jamessa/Pragmatic/Pragmatic42/MX/README.md

The Pragmatic 42 keyboard features

- 21 keys per hand with a fully symmetric double side design. One side is designed for the left hand and the other for the right.
- Duplex Matrix to save pins. Use Controller A.
-  8-pin connector that utilizes a user-friendly 2x4 2.54mm PinHeader.
- Support Kailh hotswap sockets.
- A modern 19mm x 19mm key pitch.
- Supports Kailh PG12800 Half key switch.

Current status: initing.

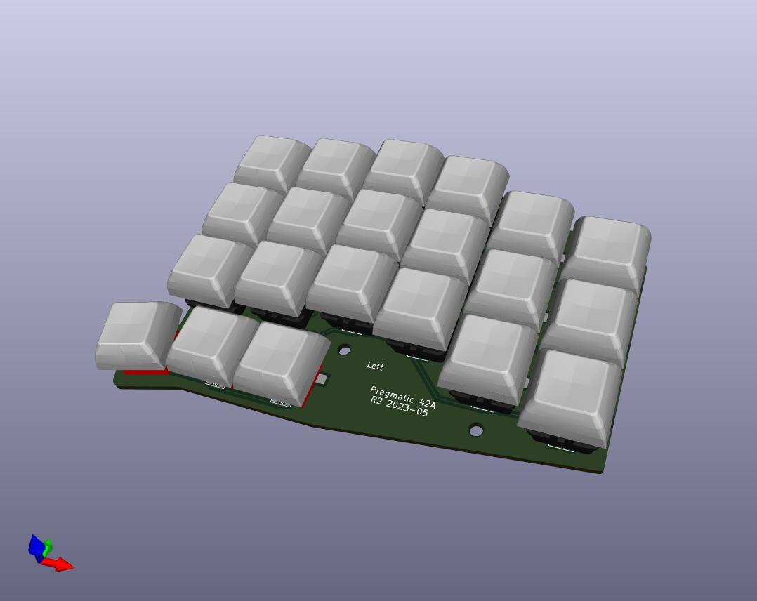
[picture p13: Pragmatic42/MX/PCB.jpg]
PCB


# Revsions
## MX42A2 2023-05-23
   ^^ Swith type MX or Choc
     ^^ Number of keys
       ^ Matrix Type: null for naïve matrix, A for duplex matrix
        ^ PCB Revision
- fix SW18, SW19 position. They were off by 0.4mm
- Stagger Profile MX V3
