jamessa/Pragmatic/layout/yapin_34/Pragmatic_60_Layer0.png

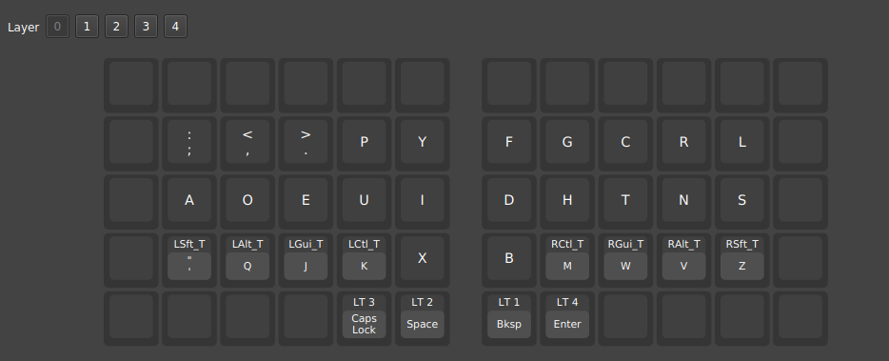
layout/yapin_34/Pragmatic_60_Layer0.png
