jamessa/Pragmatic/layout/yapin_34/Pragmatic_60_Layer1.png

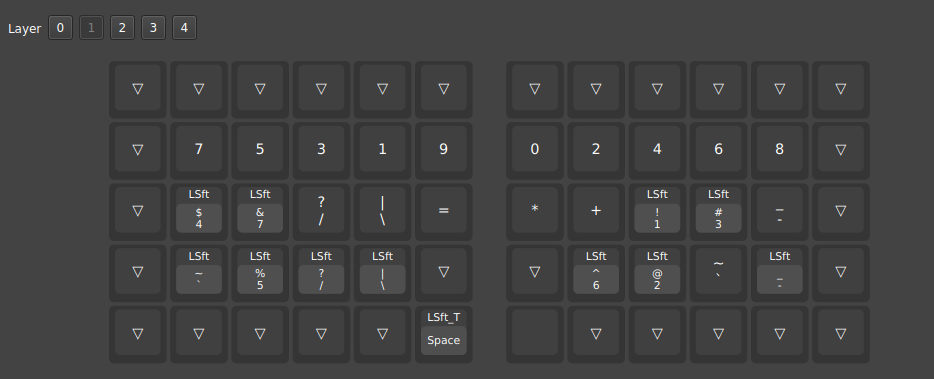
layout/yapin_34/Pragmatic_60_Layer1.png
