jamessa/Pragmatic/layout/yapin_34/Pragmatic_60_Layer2.png

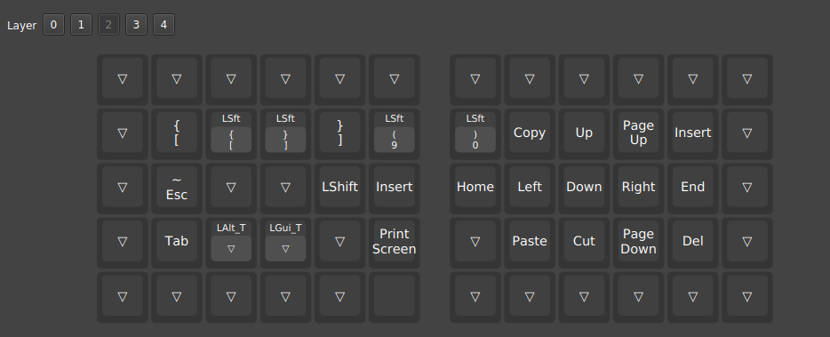
layout/yapin_34/Pragmatic_60_Layer2.png
