jamessa/Pragmatic/media/IMG_8698.jpeg

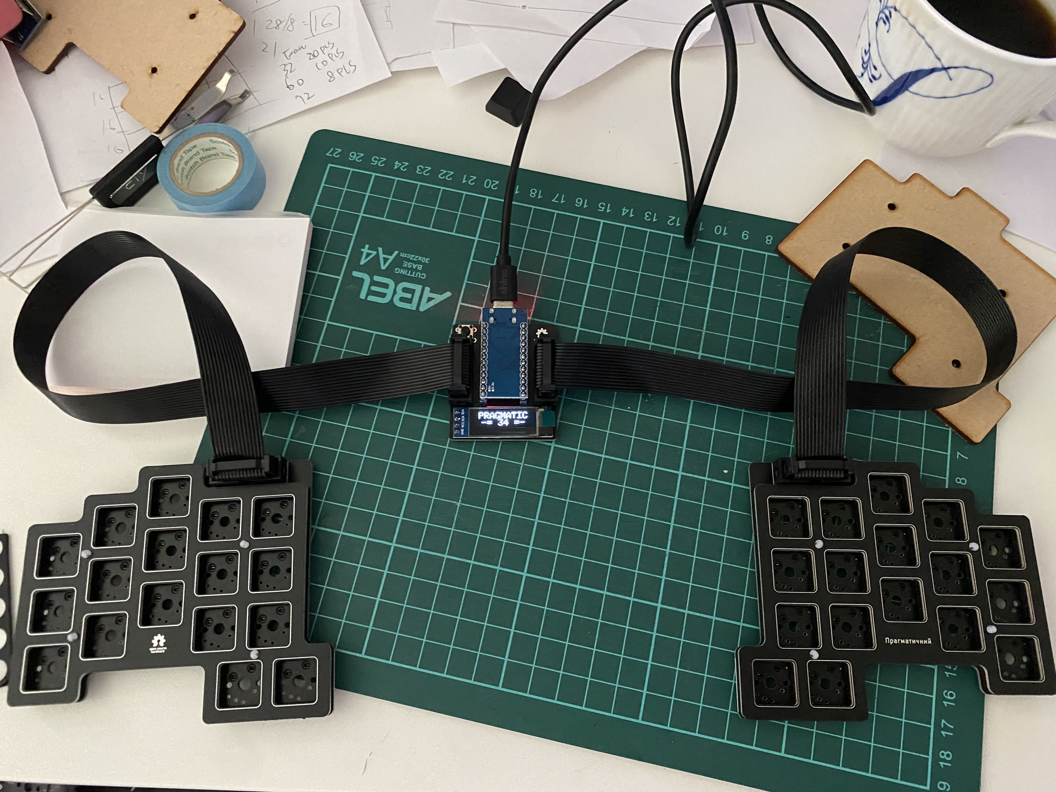
media/IMG_8698.jpeg
