jamessa/Pragmatic/media/IMG_8700.jpeg

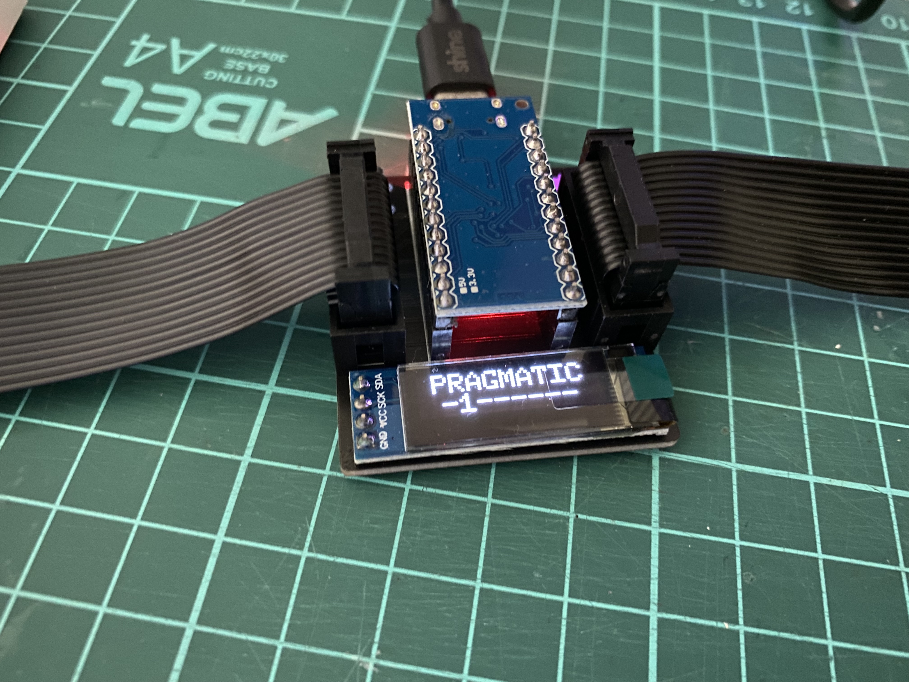
media/IMG_8700.jpeg
