jamessa/Pragmatic/media/IMG_9710.jpeg

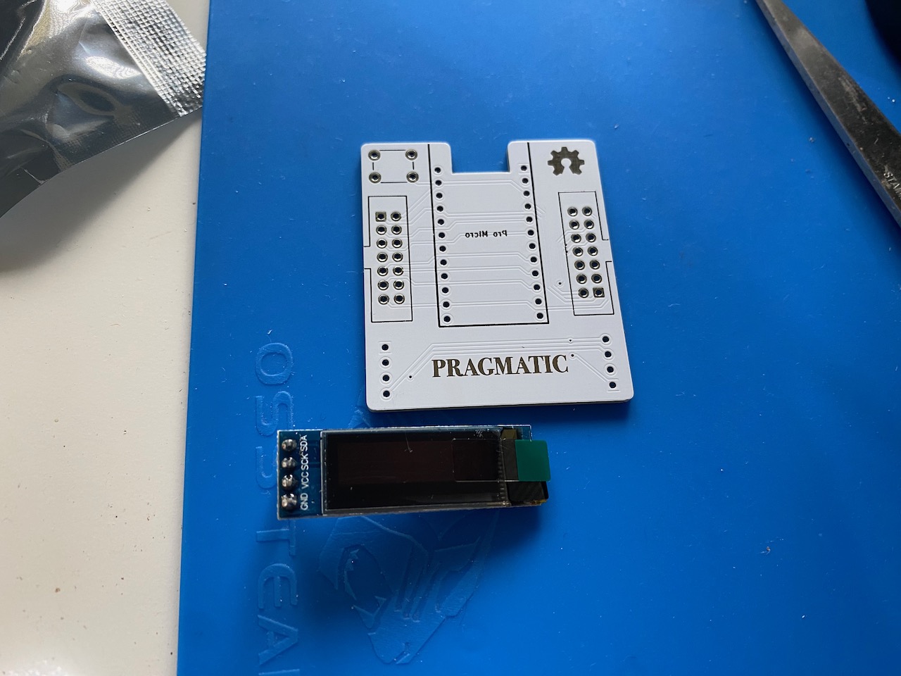
media/IMG_9710.jpeg
