jamessa/Pragmatic/media/IMG_9711.jpeg

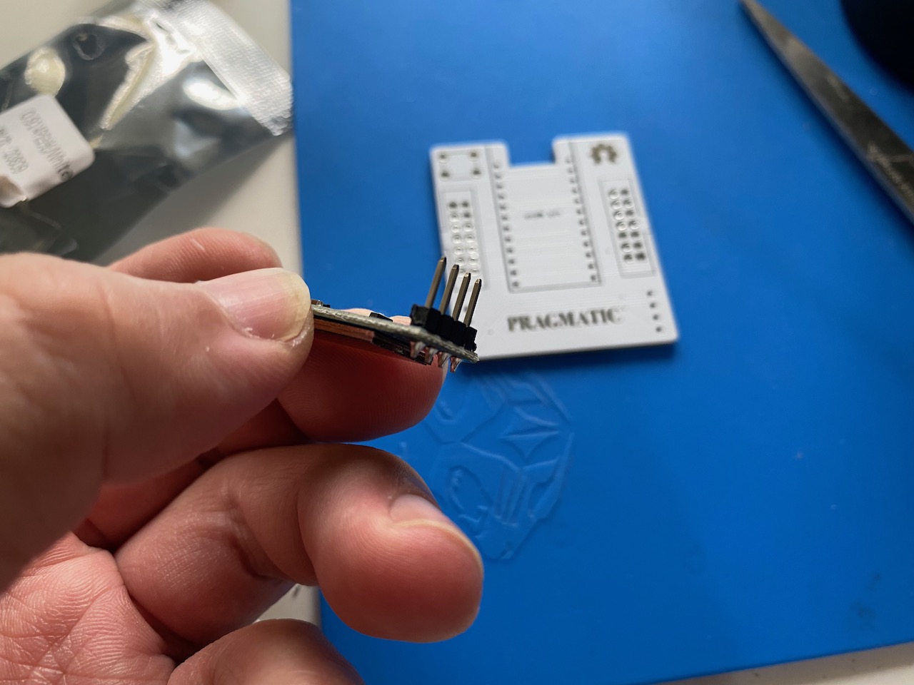
media/IMG_9711.jpeg
