jamessa/Pragmatic/media/IMG_9715.jpeg

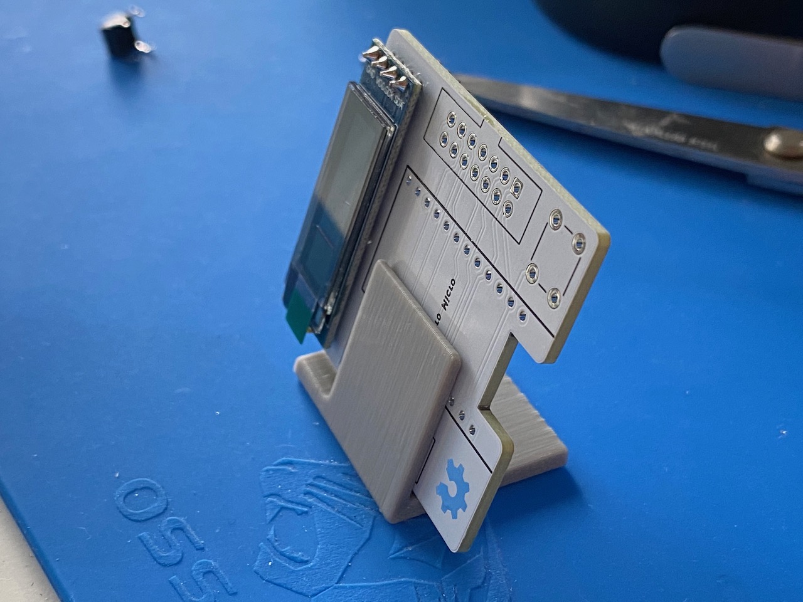
media/IMG_9715.jpeg
