jamessa/Pragmatic/media/IMG_9717.jpeg

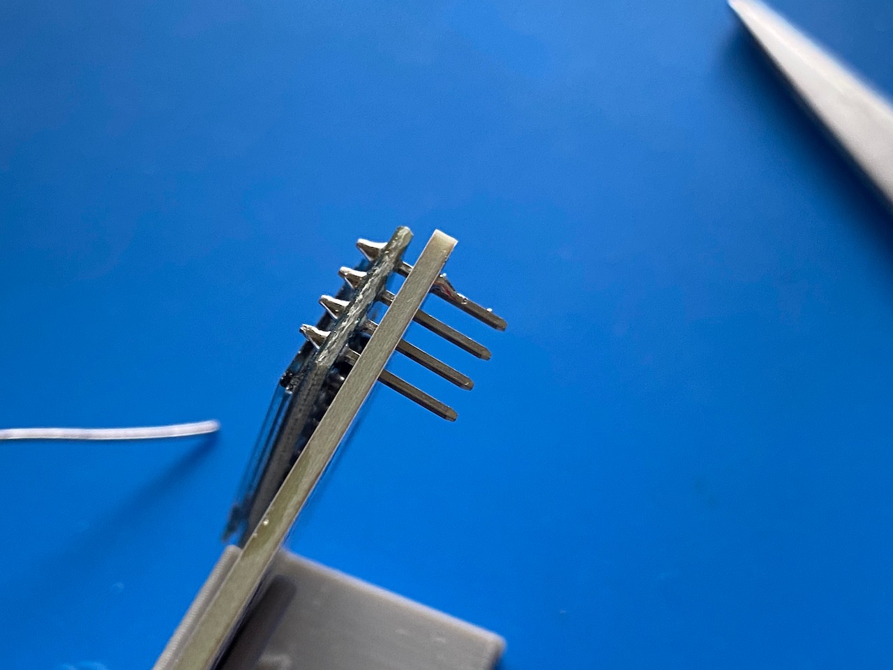
media/IMG_9717.jpeg
