jamessa/Pragmatic/media/IMG_9718.jpeg

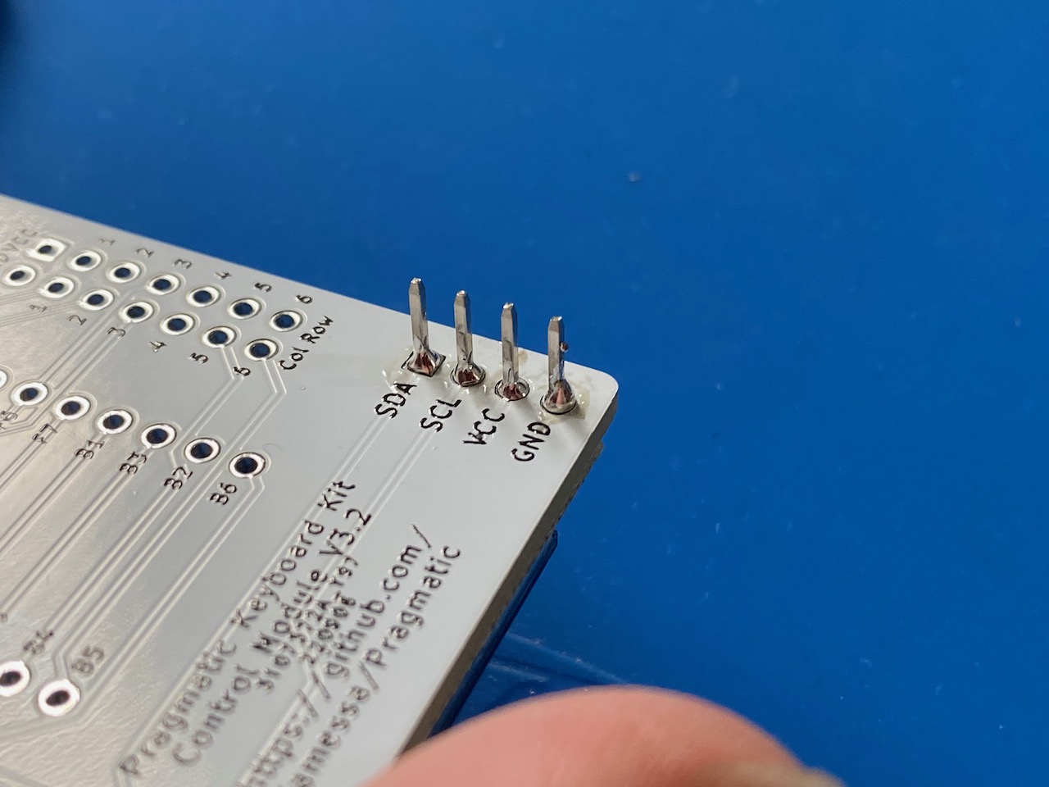
media/IMG_9718.jpeg
