jamessa/Pragmatic/media/IMG_9721.jpeg

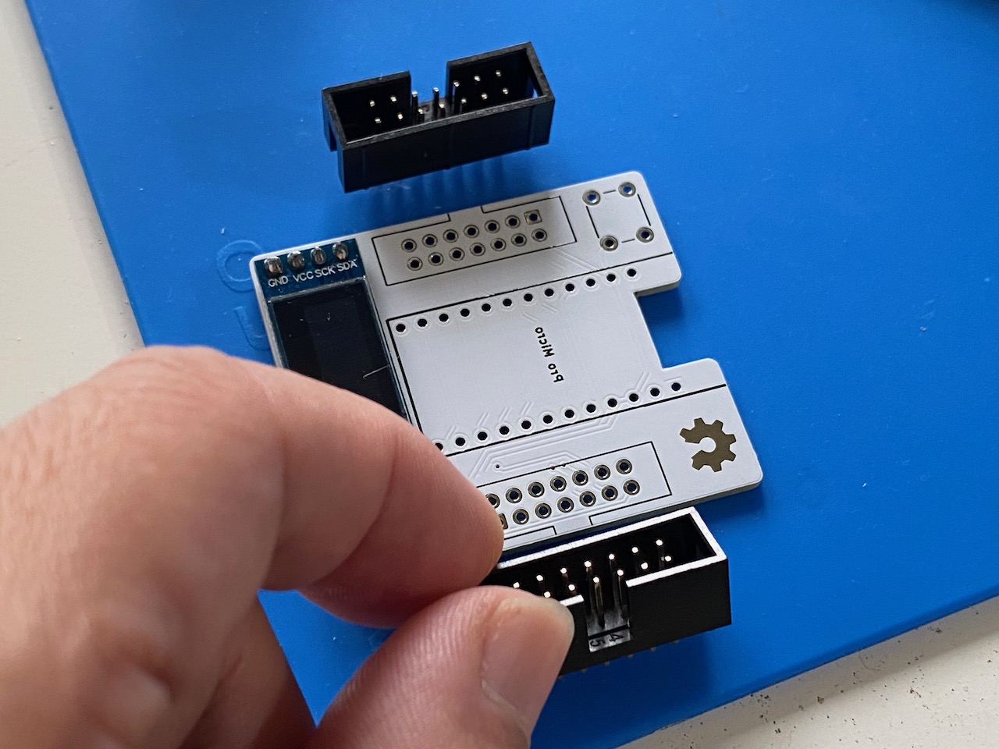
media/IMG_9721.jpeg
