jamessa/Pragmatic/media/IMG_9722.jpeg

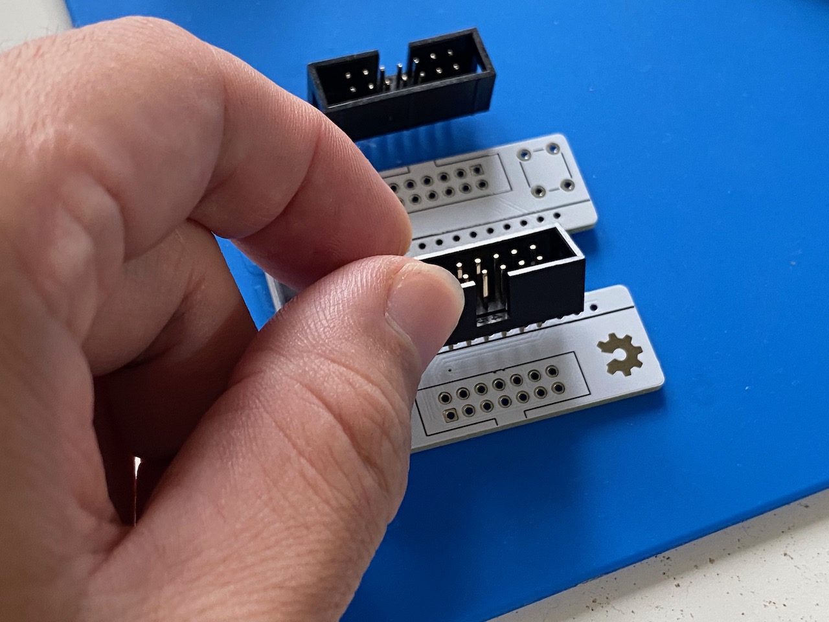
media/IMG_9722.jpeg
