jamessa/Pragmatic/media/IMG_9724.jpeg

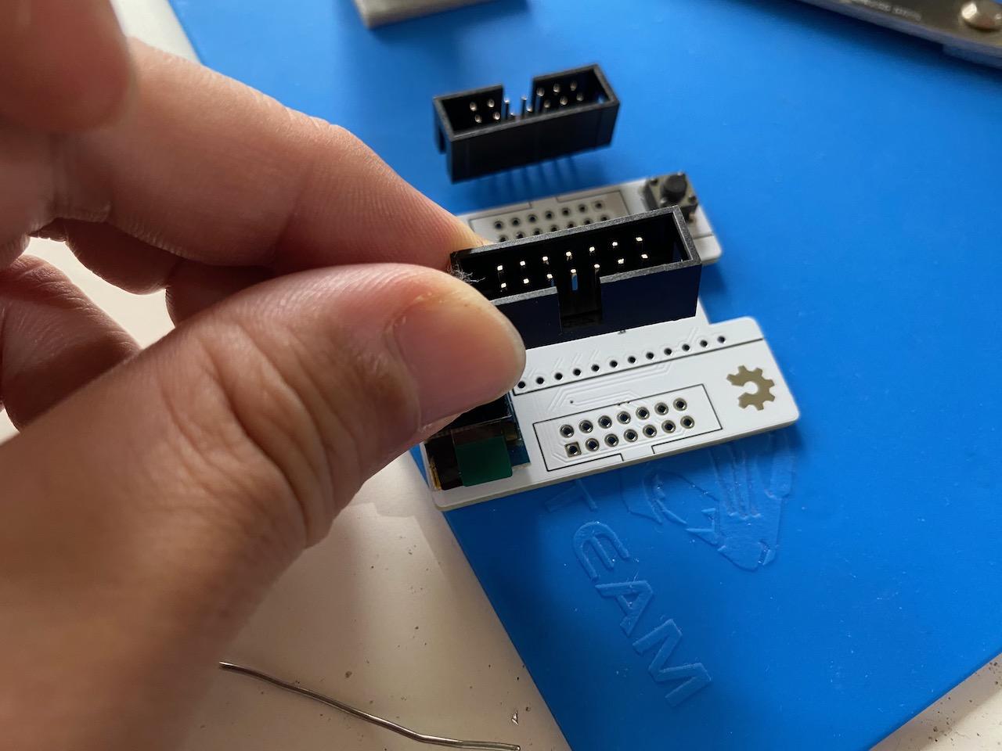
media/IMG_9724.jpeg
