jamessa/Pragmatic/media/IMG_9725.jpeg

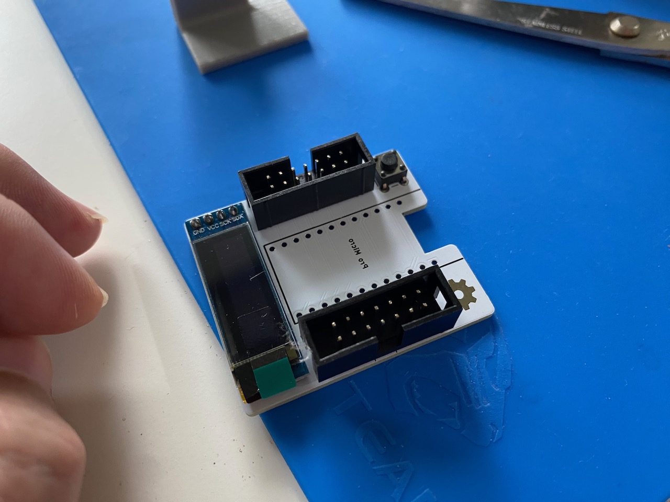
media/IMG_9725.jpeg
