jamessa/Pragmatic/media/IMG_9726.jpeg

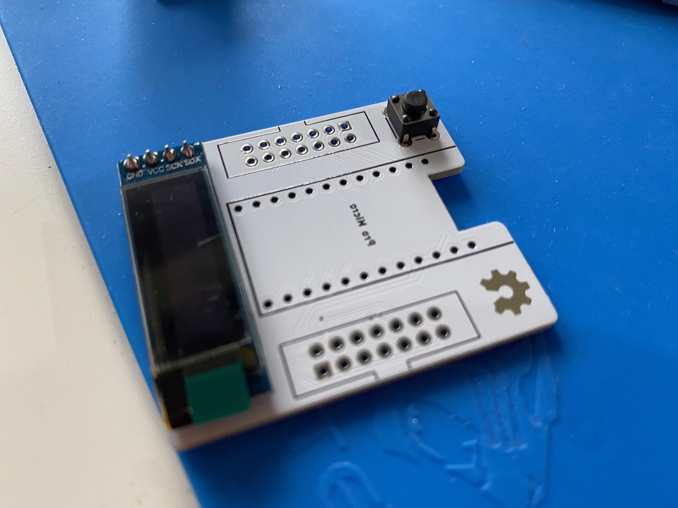
media/IMG_9726.jpeg
