jamessa/Pragmatic/media/IMG_9729.jpeg

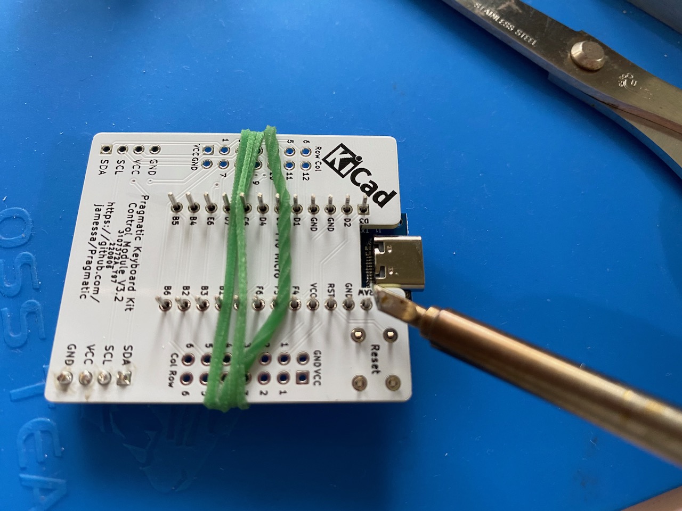
media/IMG_9729.jpeg
