jamessa/Pragmatic/media/IMG_9731.jpeg

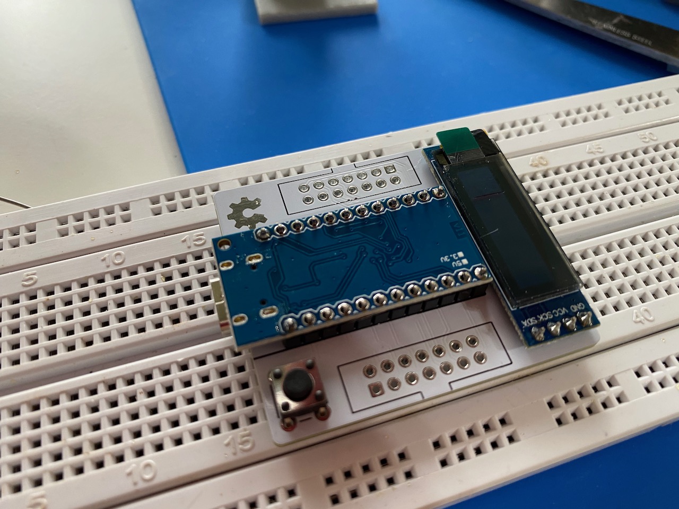
media/IMG_9731.jpeg
