jamessa/Pragmatic/media/IMG_9732.jpeg

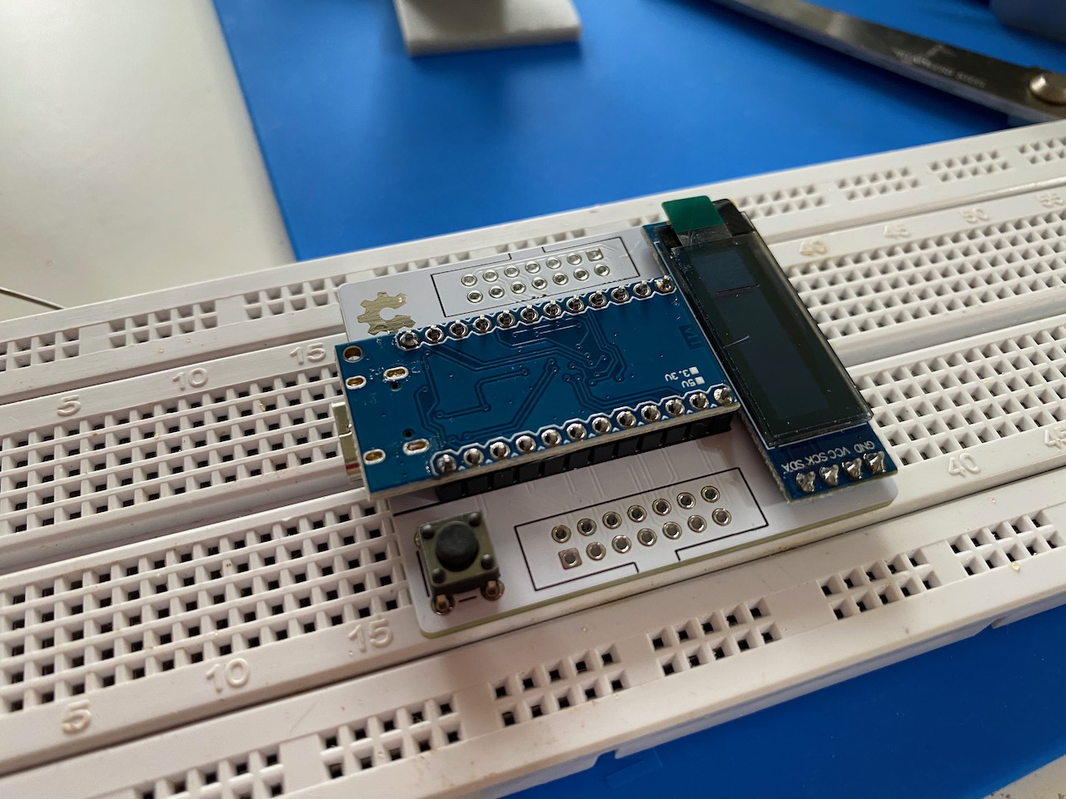
media/IMG_9732.jpeg
