jamessa/Pragmatic/media/IMG_9735.jpeg

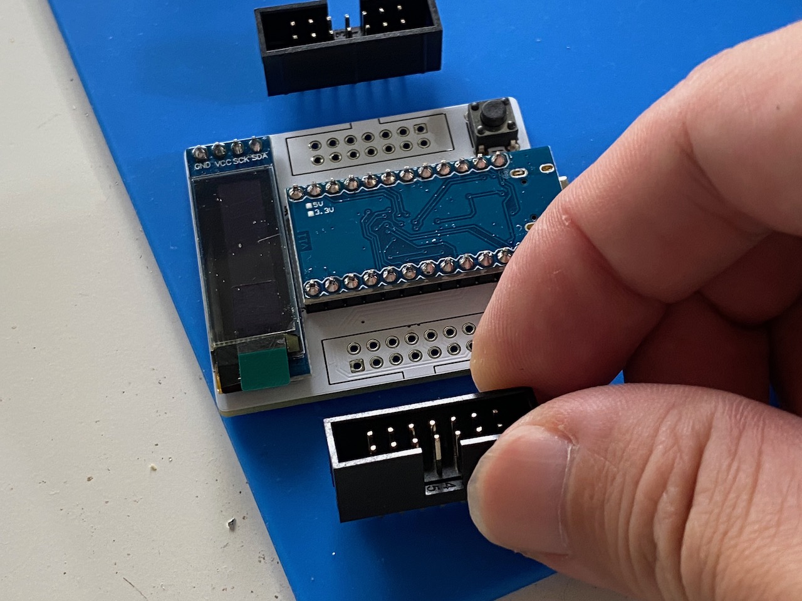
media/IMG_9735.jpeg
