jamessa/Pragmatic/media/IMG_9737.jpeg

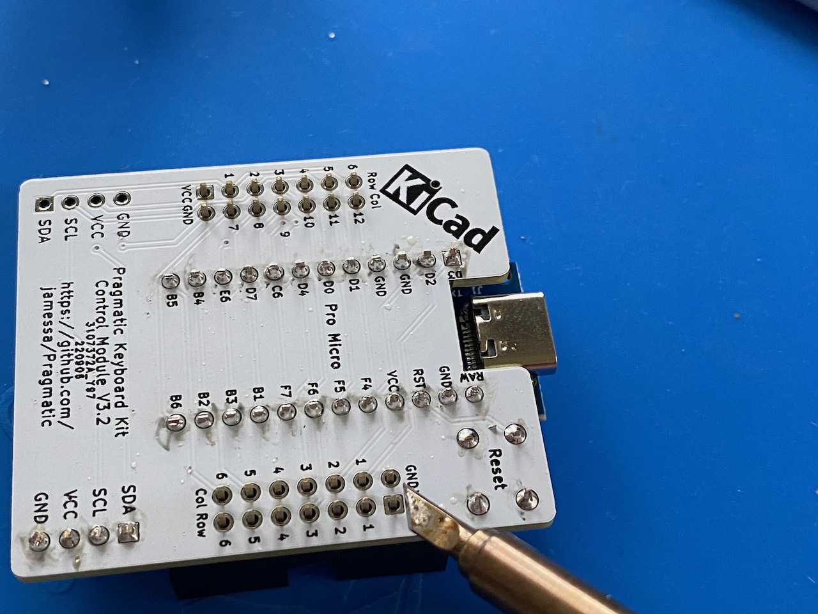
media/IMG_9737.jpeg
