jamessa/Pragmatic/media/IMG_9740.jpeg

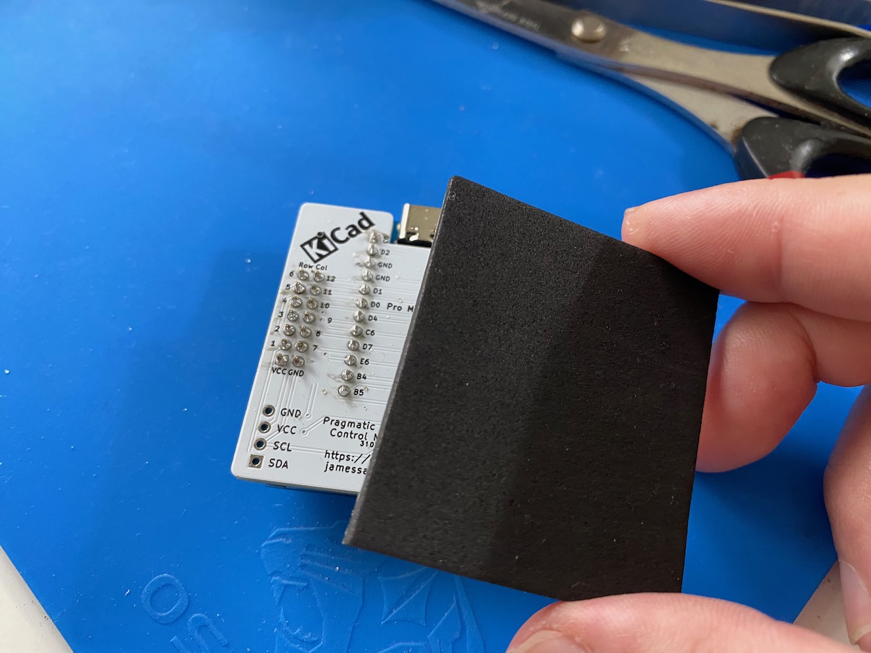
media/IMG_9740.jpeg
