jamessa/Pragmatic/media/IMG_9741.jpeg

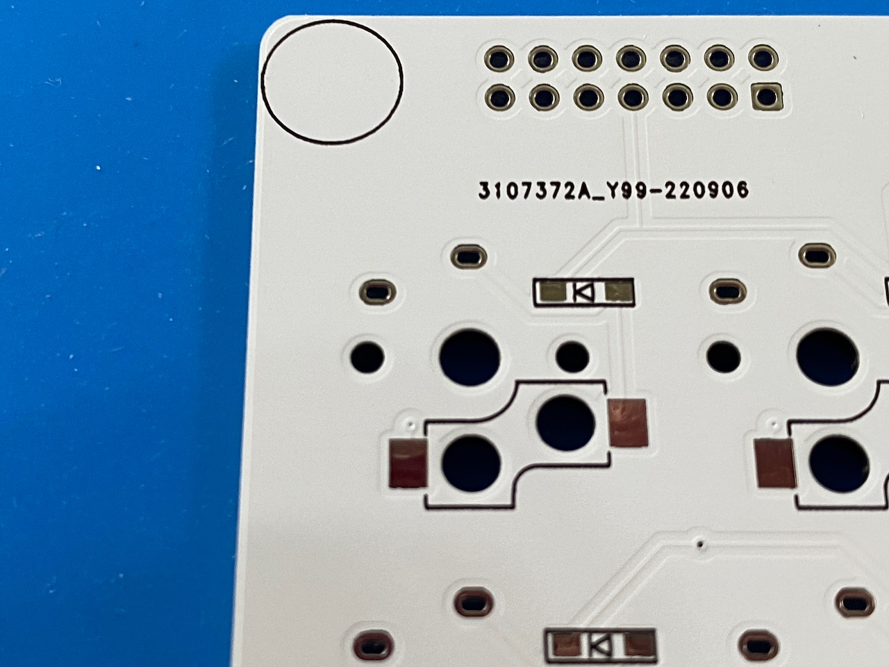
media/IMG_9741.jpeg
