jamessa/Pragmatic/media/IMG_9742.jpeg

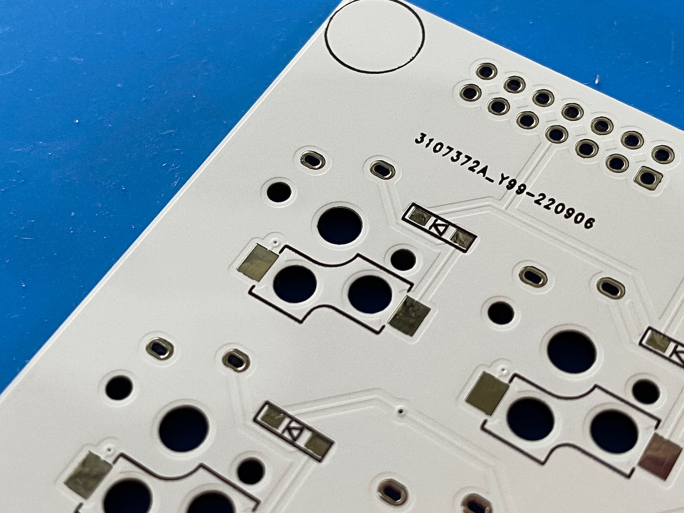
media/IMG_9742.jpeg
