jamessa/Pragmatic/media/IMG_9746.jpeg

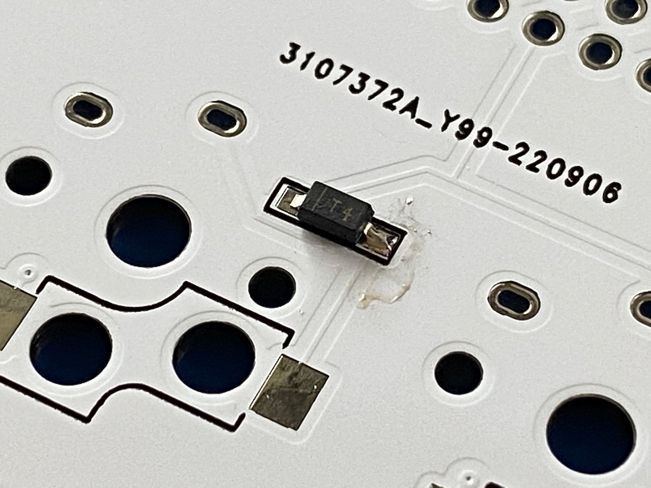
media/IMG_9746.jpeg
