jamessa/Pragmatic/media/IMG_9749.jpeg

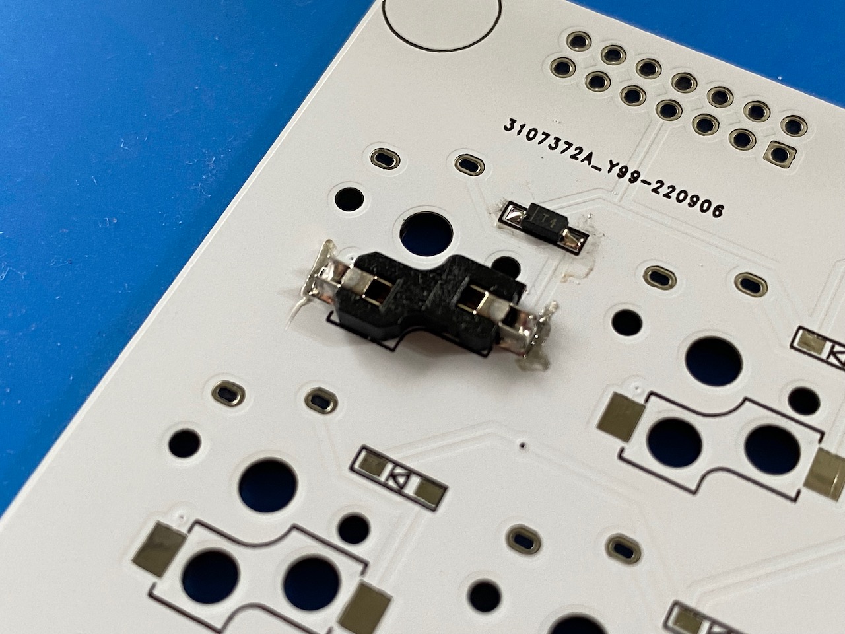
media/IMG_9749.jpeg
