jamessa/Pragmatic/media/prototype.jpeg

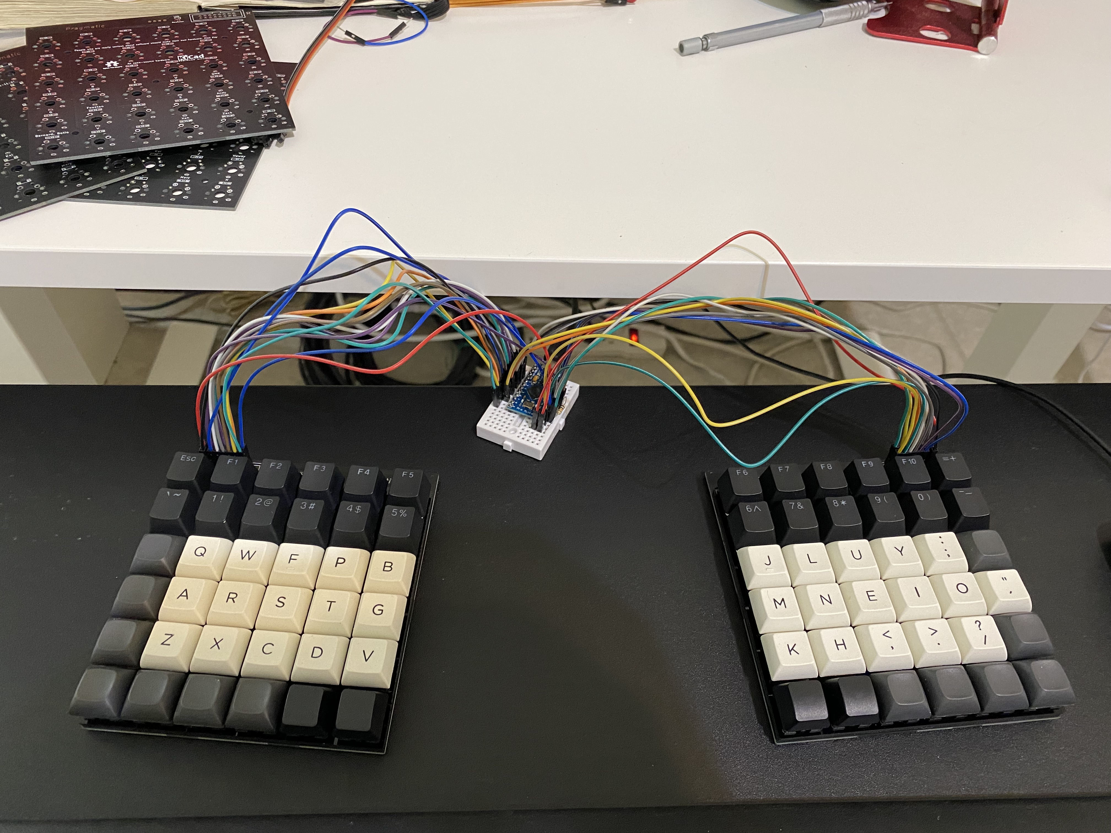
media/prototype.jpeg
