jamessa/Pragmatic/Pragmatic34/Input Choc Hotswap/Render/1.jpg

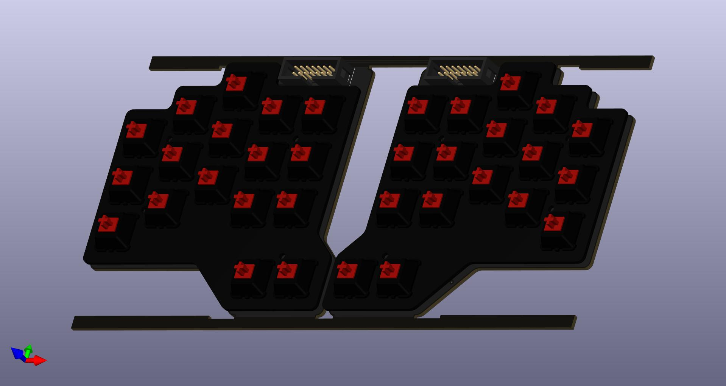
Pragmatic34/Input Choc Hotswap/Render/1.jpg
