jamessa/Pragmatic/Pragmatic34/LeftPlate/Renders/Screen Shot 2022-07-17 at 11.01.33 PM.jpg

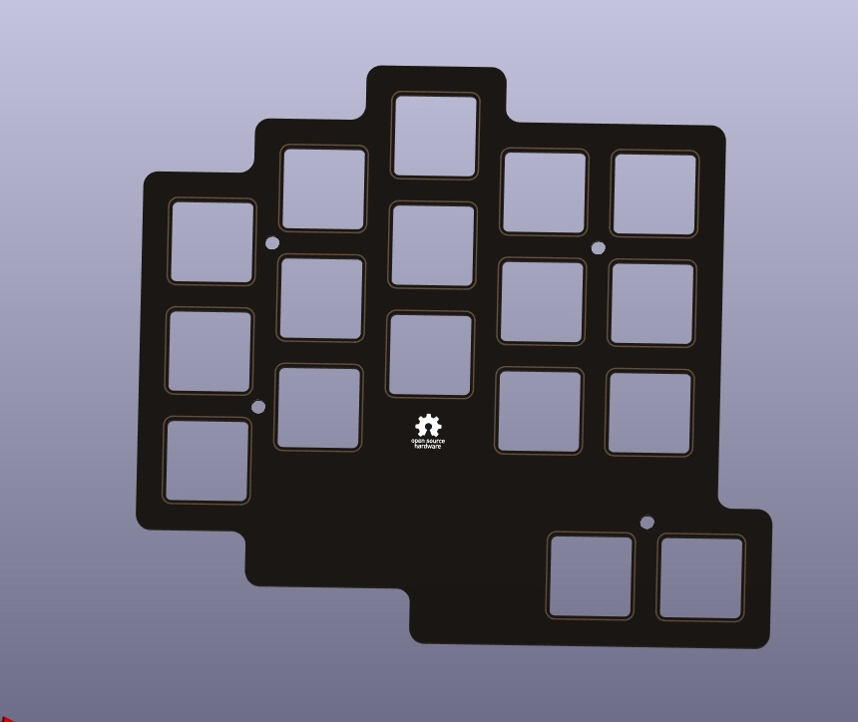
Pragmatic34/LeftPlate/Renders/Screen Shot 2022-07-17 at 11.01.33 PM.jpg
