jamessa/Pragmatic/Pragmatic34/LeftPlate/Renders/Screen Shot 2022-07-17 at 11.02.45 PM.jpg

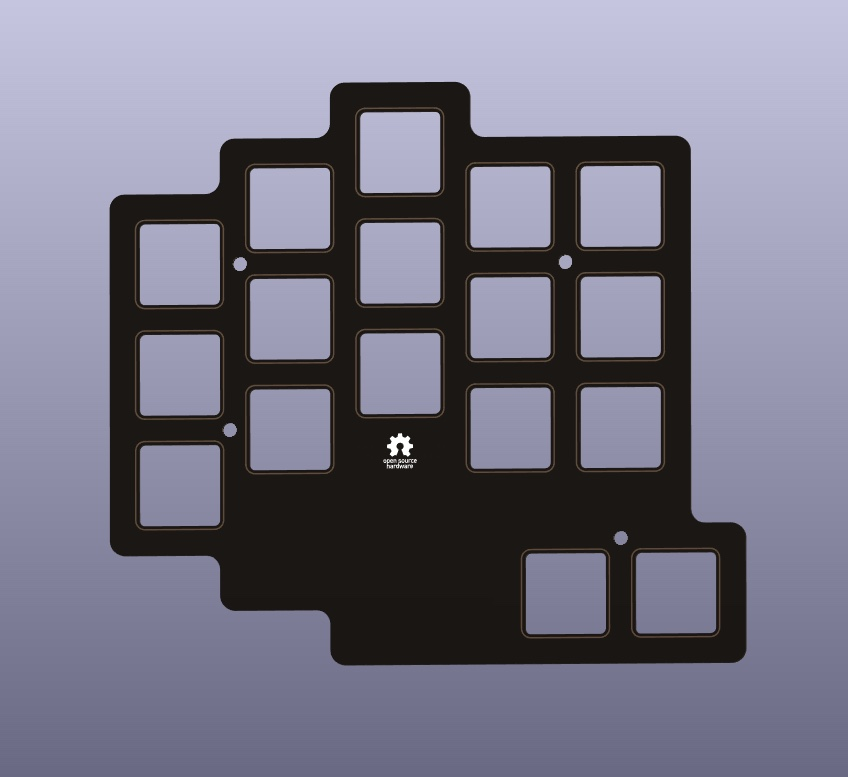
Pragmatic34/LeftPlate/Renders/Screen Shot 2022-07-17 at 11.02.45 PM.jpg
