jamessa/Pragmatic/Pragmatic36/Choc/PCB.jpg

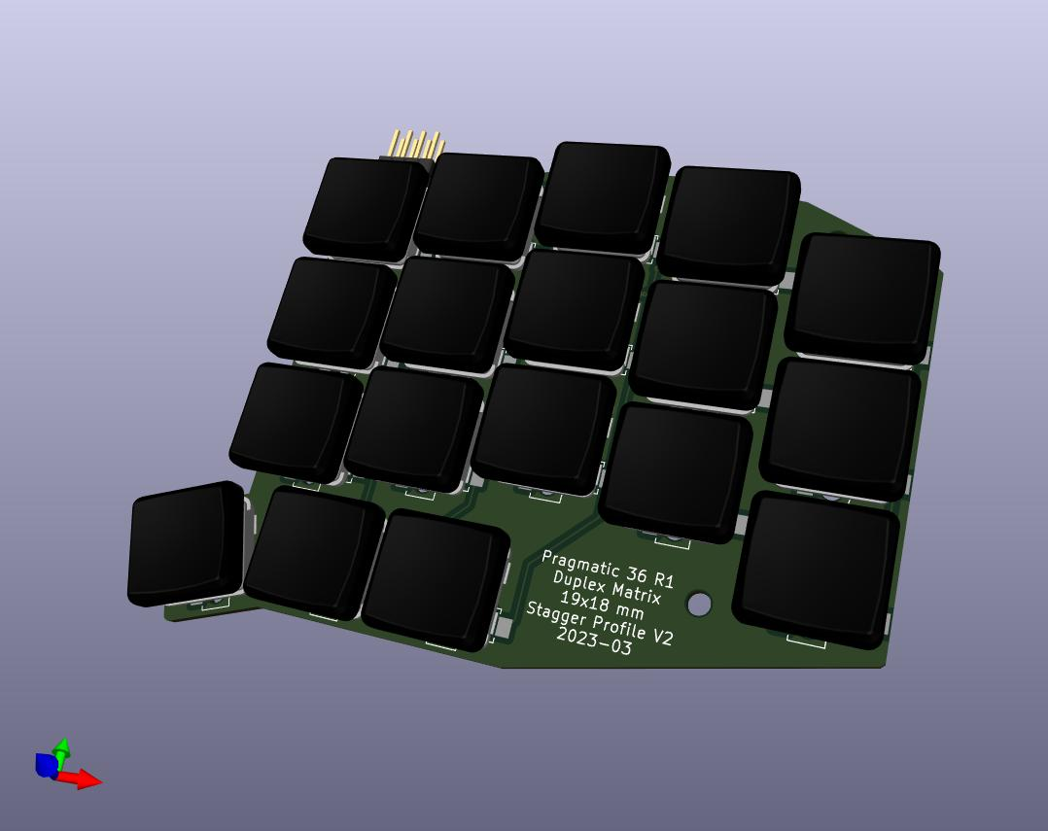
Pragmatic36/Choc/PCB.jpg
