jamessa/Pragmatic/Pragmatic56/pcb.jpg

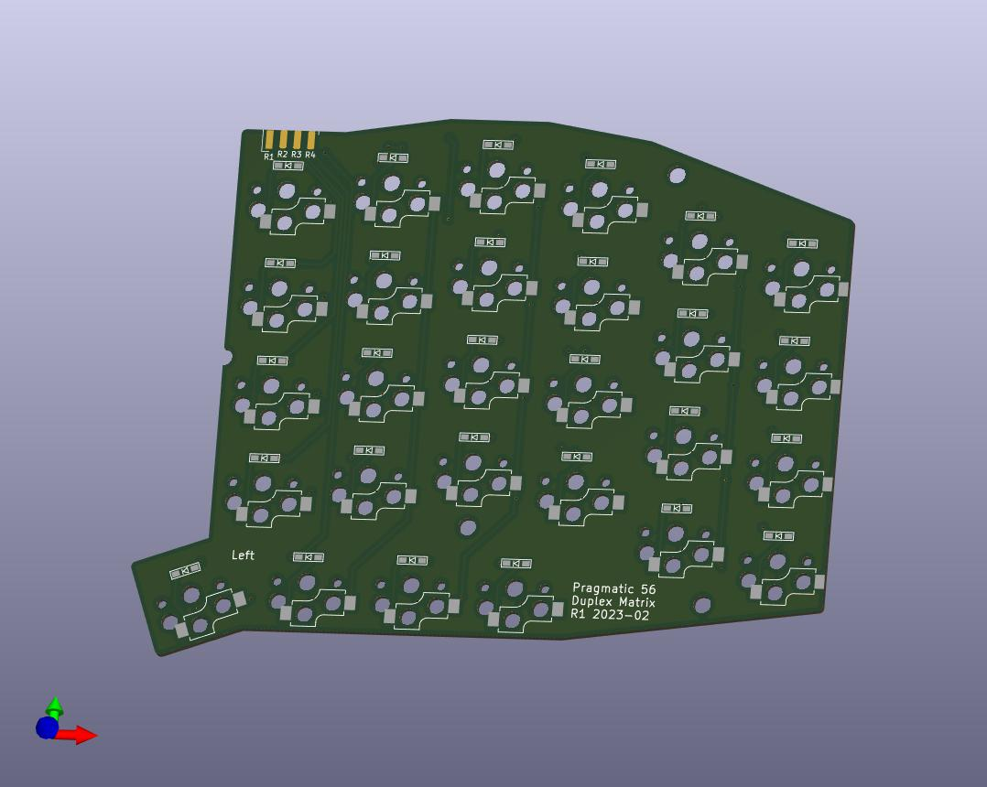
Pragmatic56/pcb.jpg
