jamessa/Pragmatic/Pragmatic56/pcbwswitch.jpg

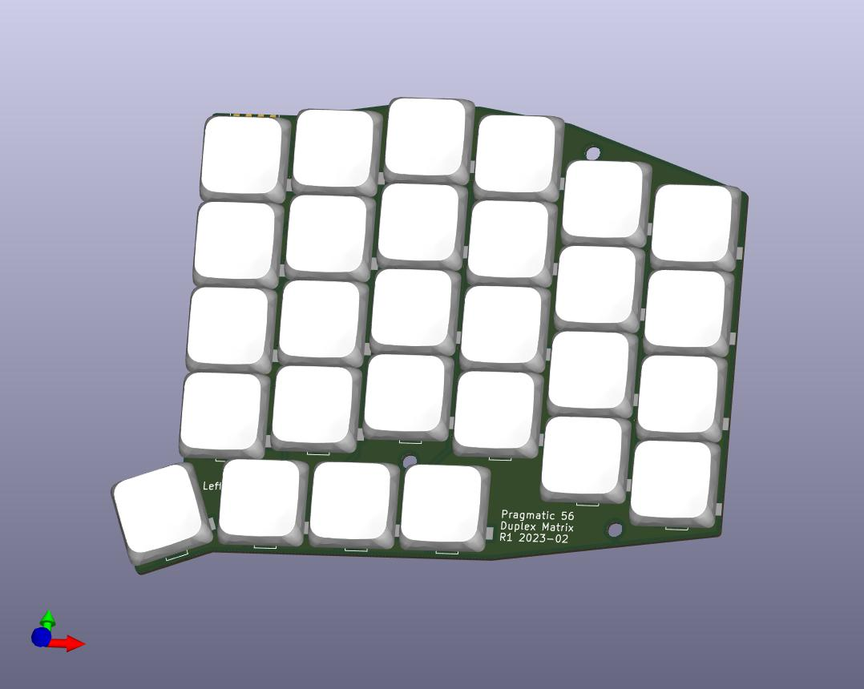
Pragmatic56/pcbwswitch.jpg
