jamessa/Pragmatic/Pragmatic60/Input 5x6 plate/Plate.jpg

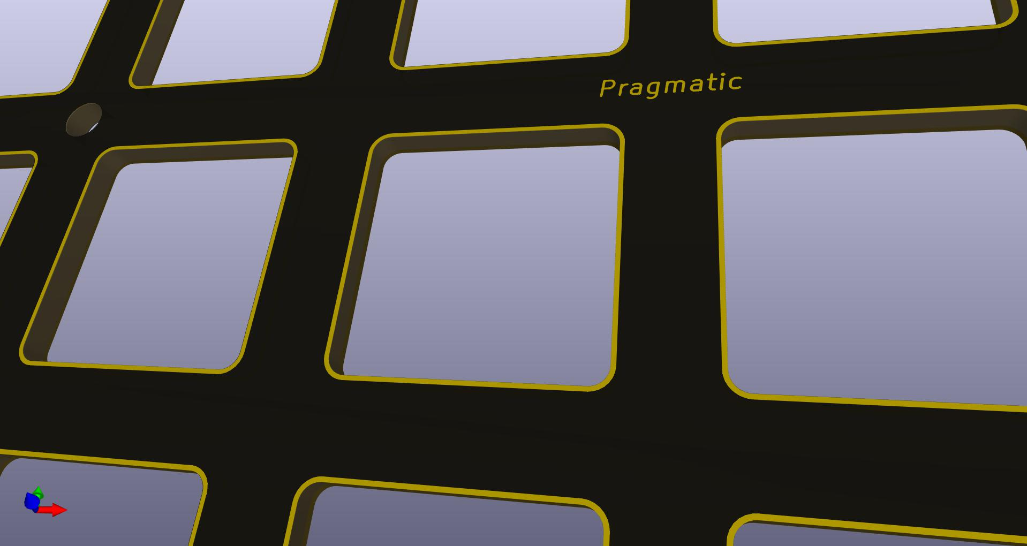
Pragmatic60/Input 5x6 plate/Plate.jpg
