jamessa/Pragmatic/Pragmatic60/Control with Type C/Control.kicad_pcb

## KiCad design Pragmatic60/Control with Type C/Control.kicad_pcb (2023-01-12, an earlier design)

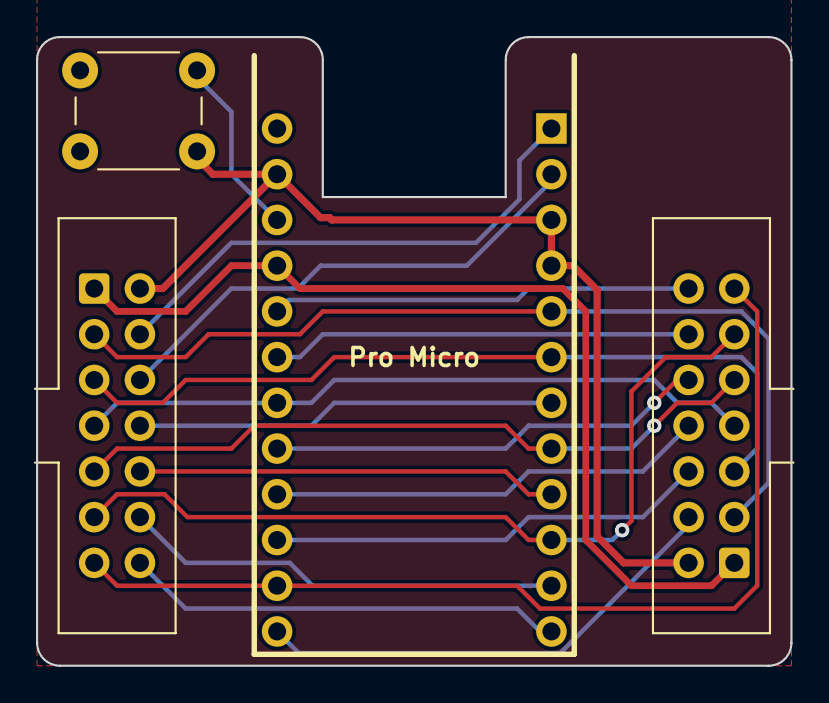
[picture p119: board Pragmatic60/Control with Type C/Control.kicad_pcb from above]

Board: 2 copper layers, 41.9 x 34.9 mm, 6 parts (1 on the bottom side), 21 nets.

Parts:
J1: L; IDC-Header_2x07_P2.54mm_Vertical
J2: R; IDC-Header_2x07_P2.54mm_Vertical
L1: JLC Legend
Logo1: OSHW-Symbol_6.7x6mm_Copper
SW1: SW_Push; SW_PUSH_6mm
U1: ProMicro; ProMicro Type C Reversed

Connections:
Col1: J1.4, U1.1 (TX0/PD3)
Col2: J1.6, U1.2 (RX1/PD2)
Col3: J1.8, U1.7 (4/PD4)
Col4: J1.10, U1.9 (6/PD7)
Col5: J1.12, U1.11 (8/PB4)
Col6: J1.14, U1.12 (9/PB5)
Col7: J2.4, U1.13 (10/PB6)
Col8: J2.6, U1.15 (14/PB3)
Col9: J2.8, U1.16 (15/PB1)
Col10: J2.10, U1.17 (A0/PF7)
Col11: J2.12, U1.19 (A2/PF5)
Col12: J2.14, U1.20 (A3/PF4)
GND: J1.2, J2.2, SW1.2, U1.3 (GND), U1.4 (GND), U1.23 (GND)
Reset: SW1.1, U1.22 (RST)
Row1: J1.3, J2.3, U1.5 (2/PD1)
Row2: J1.5, J2.5, U1.6 (3/PD0)
Row3: J1.7, J2.7, U1.18 (A1/PF6)
Row4: J1.9, J2.9, U1.8 (5/PC6)
Row5: J1.11, J2.11, U1.10 (7/PE6)
Row6: J1.13, J2.13, U1.14 (16/PB2)
VCC: J1.1, J2.1, U1.21 (VCC)
