jamessa/Pragmatic/PCB/V4/34/34.kicad_pcb

## KiCad design PCB/V4/34/34.kicad_pcb (2022-06-10)

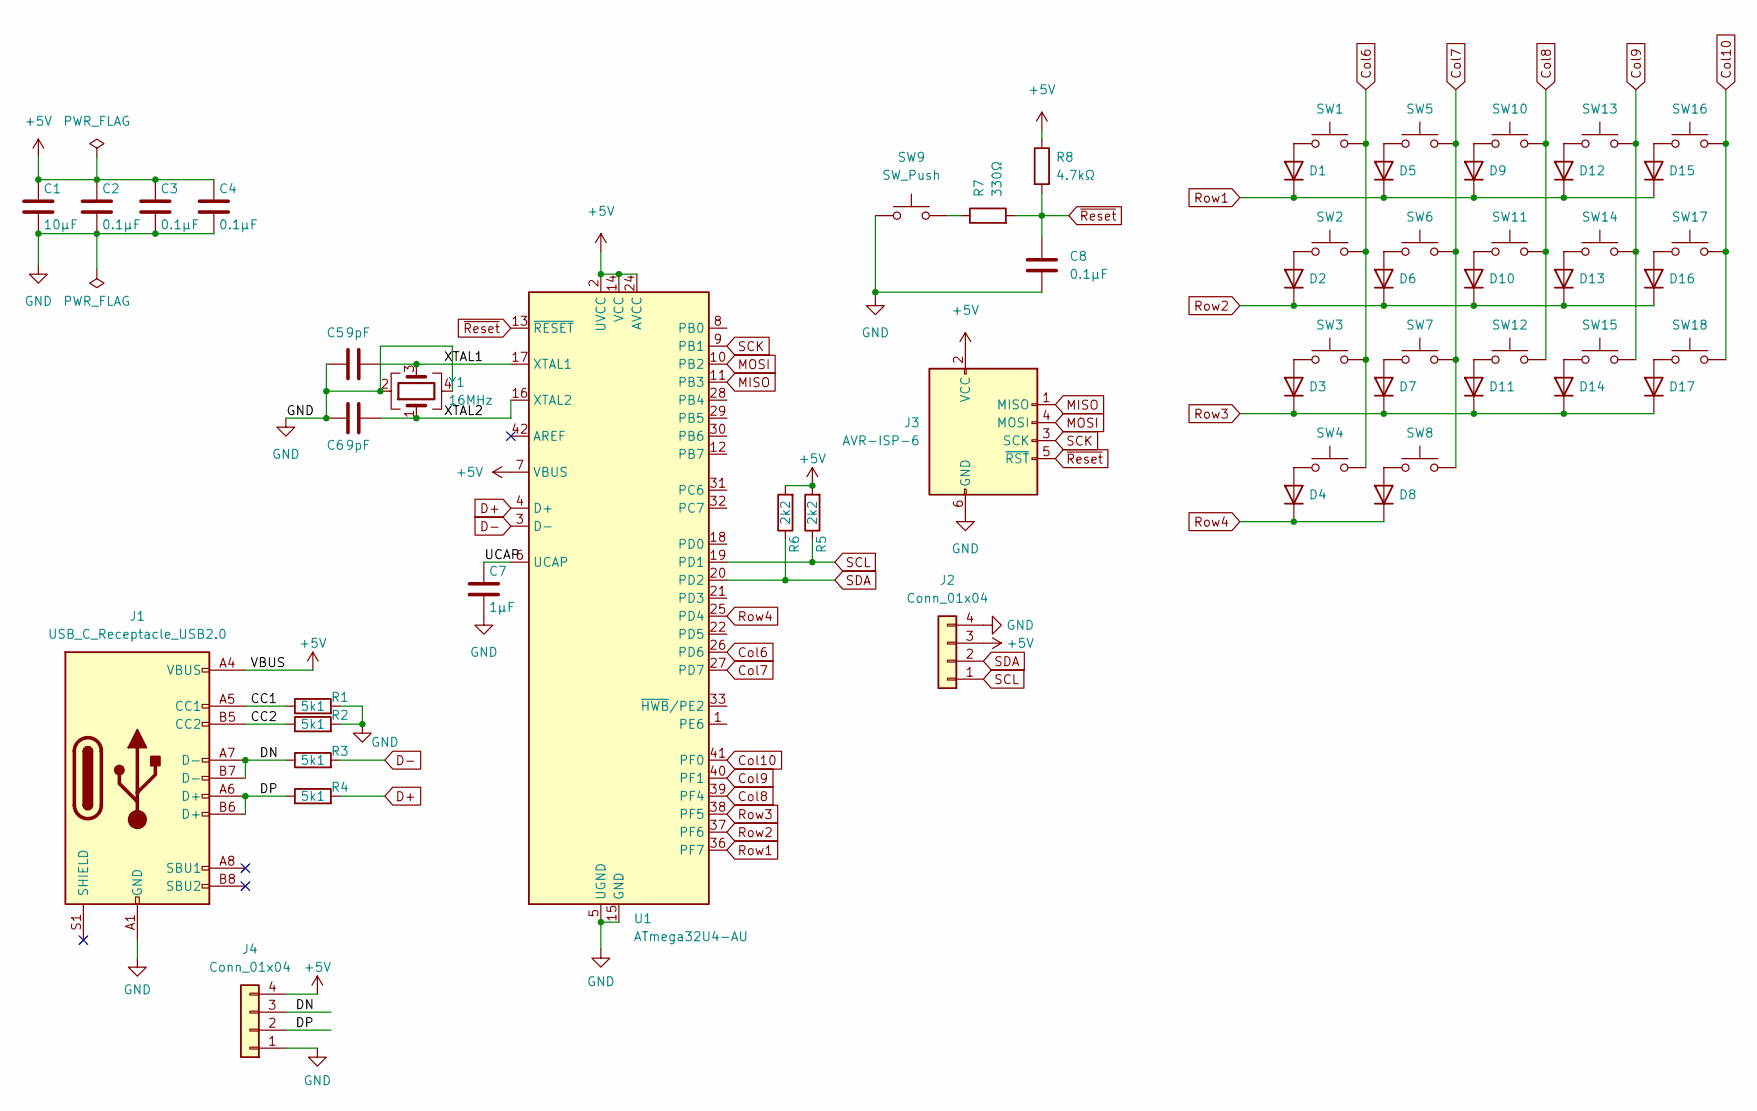
[picture p120: schematic 34.kicad_sch]

Parts:
C1: 10µF; C_0603_1608Metric_Pad1.08x0.95mm_HandSolder
C2, C3, C4, C8: 0.1µF; C_0402_1005Metric_Pad0.74x0.62mm_HandSolder
C5, C6: 9pF; C_0402_1005Metric_Pad0.74x0.62mm_HandSolder
C7: 1µF; C_0402_1005Metric_Pad0.74x0.62mm_HandSolder
D1, D2, D3, D4, D5, D6, D7, D8, D9, D10, D11, D12, D13, D14, D15, D16, D17: 1N4148; D3_SMD_v2; LCSC C81598
J1: USB_C_Receptacle_USB2.0; USB_C_Receptacle_HRO_TYPE-C-31-M-12; LCSC C165948
J2: Conn_01x04; JST_PH_S4B-PH-K_1x04_P2.00mm_Horizontal; LCSC C265452
J3: AVR-ISP-6; PinHeader_2x03_P2.54mm_Vertical
J4: Conn_01x04; USB wire pad
R1, R2, R3, R4: 5k1; R_0402_1005Metric_Pad0.72x0.64mm_HandSolder
R5, R6: 2k2; R_0402_1005Metric_Pad0.72x0.64mm_HandSolder
R7: 330Ω; R_0402_1005Metric_Pad0.72x0.64mm_HandSolder
R8: 4.7kΩ; R_0402_1005Metric_Pad0.72x0.64mm_HandSolder
SW1, SW2, SW3, SW4, SW5, SW6, SW7, SW8, SW10, SW11, SW12, SW13, SW14, SW15, SW16, SW17, SW18: SW_Push; MX_Hotswap_Choc_Solder
SW9: SW_Push; SW_SPST_SKQG_WithStem
U1: ATmega32U4-AU; TQFP-44_10x10mm_P0.8mm
Y1: 16MHz; Crystal_SMD_3225-4Pin_3.2x2.5mm; LCSC C13738

Connections:
+5V: C1.1, C2.1, C3.1, C4.1, J1.A4 (VBUS), J1.A9 (VBUS), J1.B4 (VBUS), J1.B9 (VBUS), J2.3, J3.2 (VCC), J4.4, R5.2, R6.2, R8.1, U1.2 (UVCC), U1.7 (VBUS), U1.14 (VCC), U1.24 (AVCC), U1.34 (VCC), U1.44 (AVCC)
/CC1: J1.A5 (CC1), R1.1
/CC2: J1.B5 (CC2), R2.1
/DN: J1.A7 (D-), J1.B7 (D-), J4.3, R3.1
/DP: J1.A6 (D+), J1.B6 (D+), J4.2, R4.1
/UCAP: C7.1, U1.6 (UCAP)
/XTAL1: C5.2, U1.17 (XTAL1), Y1.3
/XTAL2: C6.2, U1.16 (XTAL2), Y1.1
Col6: SW1.2, SW2.2, SW3.2, SW4.2, U1.26 (PD6)
Col7: SW5.2, SW6.2, SW7.2, SW8.2, U1.27 (PD7)
Col8: SW10.2, SW11.2, SW12.2, U1.39 (PF4)
Col9: SW13.2, SW14.2, SW15.2, U1.40 (PF1)
Col10: SW16.2, SW17.2, SW18.2, U1.41 (PF0)
D+: R4.2, U1.4 (D+)
D-: R3.2, U1.3 (D-)
GND: C1.2, C2.2, C3.2, C4.2, C5.1, C6.1, C7.2, C8.2, J1.A1 (GND), J1.A12 (GND), J1.B1 (GND), J1.B12 (GND), J2.4, J3.6 (GND), J4.1, R1.2, R2.2, SW9.1, U1.5 (UGND), U1.15 (GND), U1.23 (GND), U1.35 (GND), U1.43 (GND), Y1.2, Y1.4
MISO: J3.1 (MISO), U1.11 (PB3)
MOSI: J3.4 (MOSI), U1.10 (PB2)
unnamed: D1.2 (A), SW1.1
unnamed: D2.2 (A), SW2.1
unnamed: D3.2 (A), SW3.1
unnamed: D4.2 (A), SW4.1
unnamed: D5.2 (A), SW5.1
unnamed: D6.2 (A), SW6.1
unnamed: D7.2 (A), SW7.1
unnamed: D8.2 (A), SW8.1
unnamed: D9.2 (A), SW10.1
unnamed: D10.2 (A), SW11.1
unnamed: D11.2 (A), SW12.1
unnamed: D12.2 (A), SW13.1
unnamed: D13.2 (A), SW14.1
unnamed: D14.2 (A), SW15.1
unnamed: D15.2 (A), SW16.1
unnamed: D16.2 (A), SW17.1
unnamed: D17.2 (A), SW18.1
unnamed: R7.1, SW9.2
Row1: D1.1 (K), D5.1 (K), D9.1 (K), D12.1 (K), D15.1 (K), U1.36 (PF7)
Row2: D2.1 (K), D6.1 (K), D10.1 (K), D13.1 (K), D16.1 (K), U1.37 (PF6)
Row3: D3.1 (K), D7.1 (K), D11.1 (K), D14.1 (K), D17.1 (K), U1.38 (PF5)
Row4: D4.1 (K), D8.1 (K), U1.25 (PD4)
SCK: J3.3 (SCK), U1.9 (PB1)
SCL: J2.1, R6.1, U1.19 (PD1)
SDA: J2.2, R5.1, U1.20 (PD2)
~Reset: C8.1, J3.5 (~RST), R7.2, R8.2, U1.13 (~RESET)

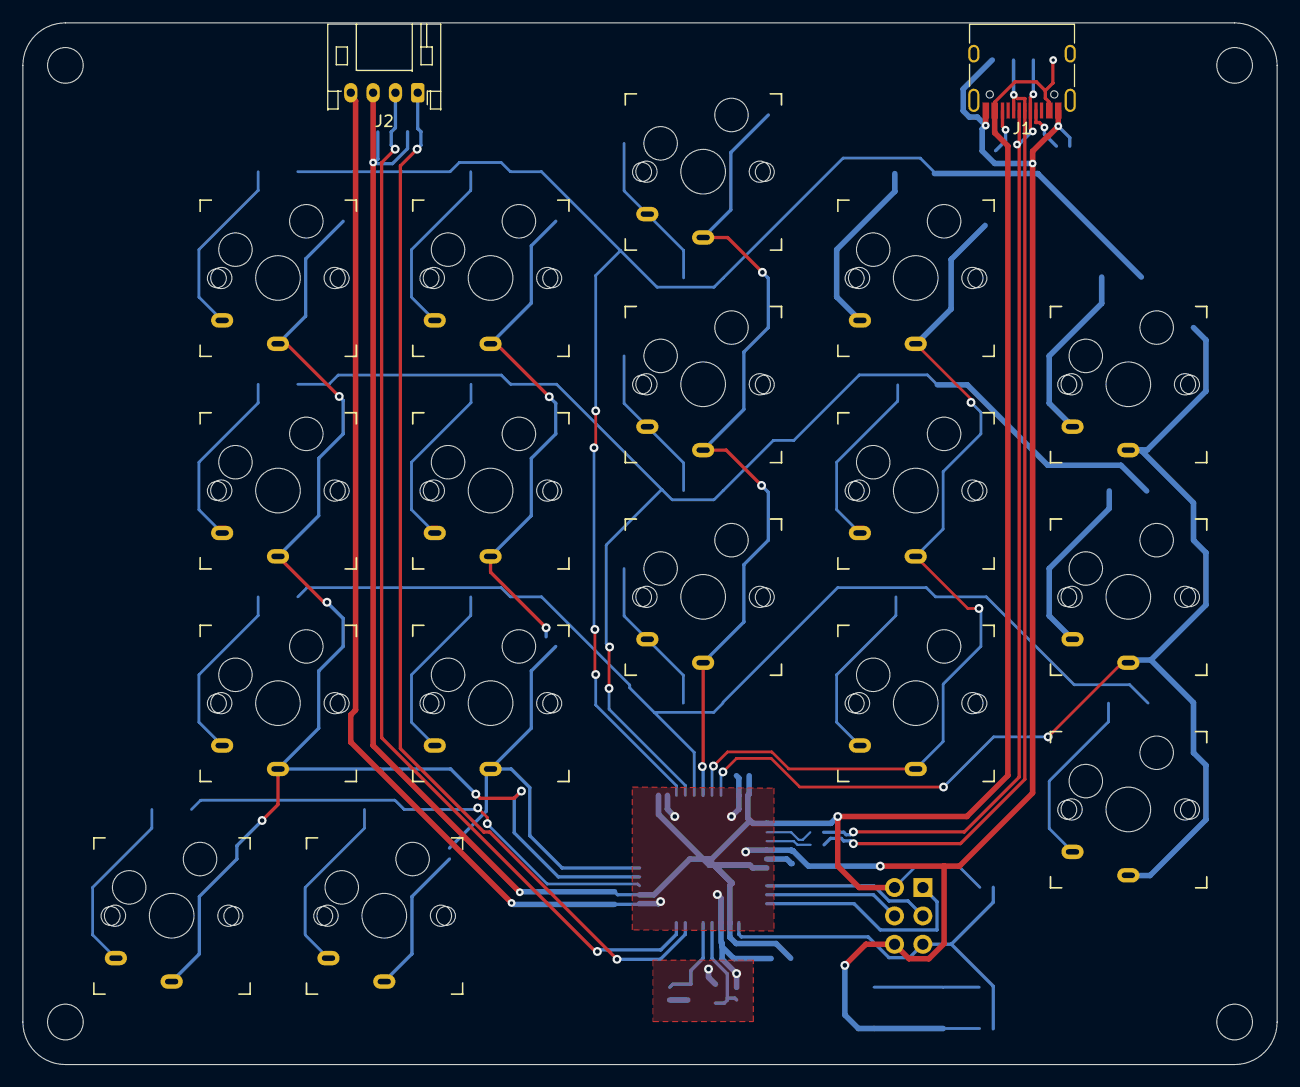
[picture p121: board 34.kicad_pcb from above]

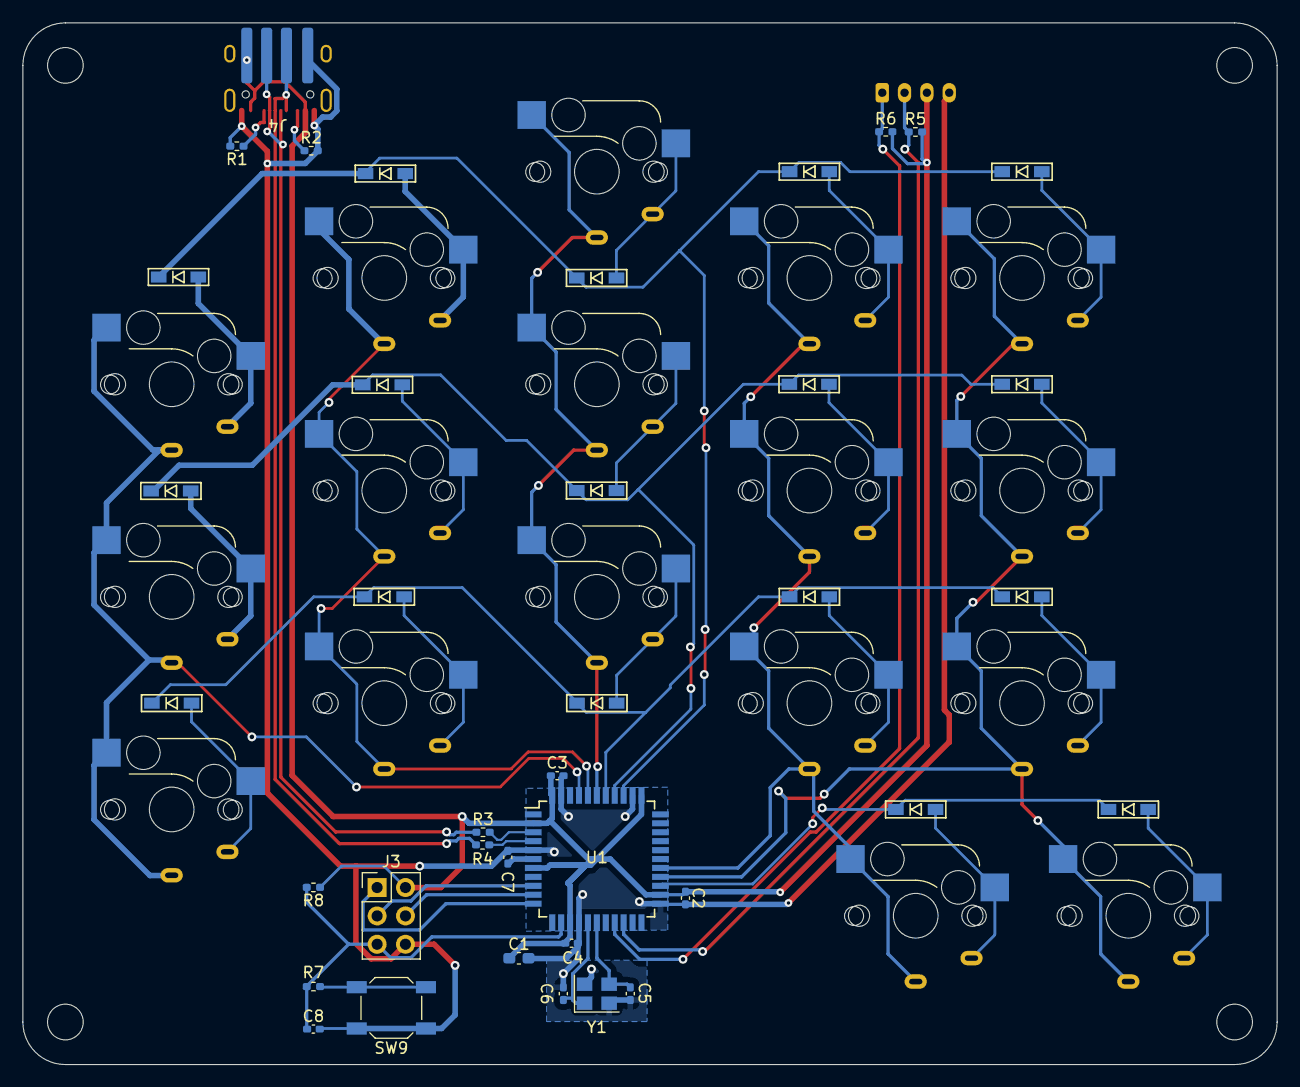
[picture p122: board 34.kicad_pcb from below]

Board: 2 copper layers, 112.4 x 93.3 mm, 57 parts (38 on the bottom side), 44 nets.
